skksn1230/raft21/image/PCB1.jpeg

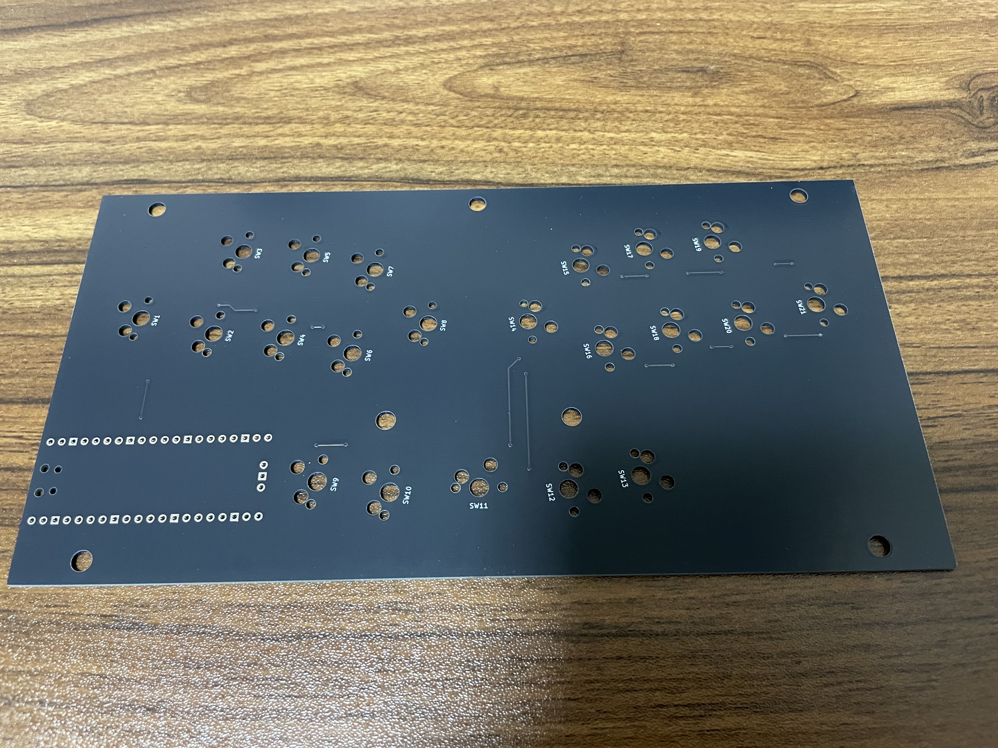
image/PCB1.jpeg
